huming2207/kcloud-intelliplant/ArduinoNode/Barometer.ino

/* 
    SHSS KCloud IntelliPlant  Node source code
    Author: Jackson Ming Hu <huming2207@gmail.com>
            Technical Club Union of Shenzhen Highschool of Science
            ...and some unknown guys including the TAOBAO retailers, thanks them!!
			深圳科学高中 科高云子项目 智慧农业物联网灌溉机
			深圳科学高中技术类社团联合会自动化电子项目组
			程序作者：胡铭 huming2207@gmail.com
			
    ***THIS CODE IS PROTECTED BY LGPL LICENCE, FOR NON-COMMERCIAL USE ONLY! ***
        本程序受LGPL协议保护，严禁商用。
    Barometer.ino -->> A tiny BOSCH BMP085/180 barometer library
                       Ported from Mosquito Multi Ground station project
                       Originally from the retailer's AVR example source code.
                       Compared with other BMP085/180 barometer libraries, this library uses less RAM and has a better performance.
					   来自淘宝奸商AVR程序精简改进的博世BMP085/180气压计类库，迁移自蚊子地面站项目，
					   相比其他Arduino的博世气压计库，它更节约存储空间和内存。
                       
*/
void bmp085Calibration()
{
  ac1 = bmp085ReadInt(0xAA);
  ac2 = bmp085ReadInt(0xAC);
  ac3 = bmp085ReadInt(0xAE);
  ac4 = bmp085ReadInt(0xB0);
  ac5 = bmp085ReadInt(0xB2);
  ac6 = bmp085ReadInt(0xB4);
  b1 = bmp085ReadInt(0xB6);
  b2 = bmp085ReadInt(0xB8);
  mb = bmp085ReadInt(0xBA);
  mc = bmp085ReadInt(0xBC);
  md = bmp085ReadInt(0xBE);
}

float bmp085GetTemperature(unsigned int ut){
  long x1, x2;

  x1 = (((long)ut - (long)ac6)*(long)ac5) >> 15;
  x2 = ((long)mc << 11)/(x1 + md);
  b5 = x1 + x2;

  float temp = ((b5 + 8)>>4);
  temp = temp /10;

  return temp;
}


long bmp085GetPressure(unsigned long up){
  long x1, x2, x3, b3, b6, p;
  unsigned long b4, b7;

  b6 = b5 - 4000;
  x1 = (b2 * (b6 * b6)>>12)>>11;
  x2 = (ac2 * b6)>>11;
  x3 = x1 + x2;
  b3 = (((((long)ac1)*4 + x3)<<OSS) + 2)>>2;

  x1 = (ac3 * b6)>>13;
  x2 = (b1 * ((b6 * b6)>>12))>>16;
  x3 = ((x1 + x2) + 2)>>2;
  b4 = (ac4 * (unsigned long)(x3 + 32768))>>15;

  b7 = ((unsigned long)(up - b3) * (50000>>OSS));
  if (b7 < 0x80000000)
    p = (b7<<1)/b4;
  else
    p = (b7/b4)<<1;

  x1 = (p>>8) * (p>>8);
  x1 = (x1 * 3038)>>16;
  x2 = (-7357 * p)>>16;
  p += (x1 + x2 + 3791)>>4;

  long baro;
  unsigned long i;
  unsigned long filter_sum = 0;
  for (i = 0; i < 5; i++) {
	  filter_sum += p;
	  delay(1);
  }
  baro = long(filter_sum / 5);
  return baro;
}

char bmp085Read(unsigned char address)
{
  Wire.beginTransmission(BMP085_ADDRESS);
  Wire.write(address);
  Wire.endTransmission();

  Wire.requestFrom(BMP085_ADDRESS, 1);
  while(!Wire.available());

  return Wire.read();
}

int bmp085ReadInt(unsigned char address)
{
  unsigned char msb, lsb;

  Wire.beginTransmission(BMP085_ADDRESS);
  Wire.write(address);
  Wire.endTransmission();

  Wire.requestFrom(BMP085_ADDRESS, 2);
  while(Wire.available()<2)
    ;
  msb = Wire.read();
  lsb = Wire.read();

  return (int) msb<<8 | lsb;
}


unsigned int bmp085ReadUT(){
  unsigned int ut;

  // Write 0x2E into Register 0xF4
  // This requests a temperature reading
  Wire.beginTransmission(BMP085_ADDRESS);
  Wire.write(0xF4);
  Wire.write(0x2E);
  Wire.endTransmission();

  // Wait at least 4.5ms
  delay(5);

  // Read two bytes from registers 0xF6 and 0xF7
  ut = bmp085ReadInt(0xF6);
  return ut;
}

  // Read the uncompensated pressure value
  unsigned long bmp085ReadUP(){

  unsigned char msb, lsb, xlsb;
  unsigned long up = 0;

  // Write 0x34+(OSS<<6) into register 0xF4
  // Request a pressure reading w/ oversampling setting
  Wire.beginTransmission(BMP085_ADDRESS);
  Wire.write(0xF4);
  Wire.write(0x34 + (OSS<<6));
  Wire.endTransmission();

  // Wait for conversion, delay time dependent on OSS
  delay(2 + (3<<OSS));

  // Read register 0xF6 (MSB), 0xF7 (LSB), and 0xF8 (XLSB)
  msb = bmp085Read(0xF6);
  lsb = bmp085Read(0xF7);
  xlsb = bmp085Read(0xF8);

  up = (((unsigned long) msb << 16) | ((unsigned long) lsb << 8) | (unsigned long) xlsb) >> (8-OSS);

  return up;
}

void writeRegister(int deviceAddress, byte address, byte val) {
  Wire.beginTransmission(deviceAddress); // start transmission to device 
  Wire.write(address);       // send register address
  Wire.write(val);         // send value to write
  Wire.endTransmission();     // end transmission
}

int readRegister(int deviceAddress, byte address){

  int v;
  Wire.beginTransmission(deviceAddress);
  Wire.write(address); // register to read
  Wire.endTransmission();

  Wire.requestFrom(deviceAddress, 1); // read a byte

  while(!Wire.available()) {
    // waiting
  }

  v = Wire.read();
  return v;
}
